rganlath3/PCB-Business-Card/Visual_Assetts/EnclosureUnpopulated.png

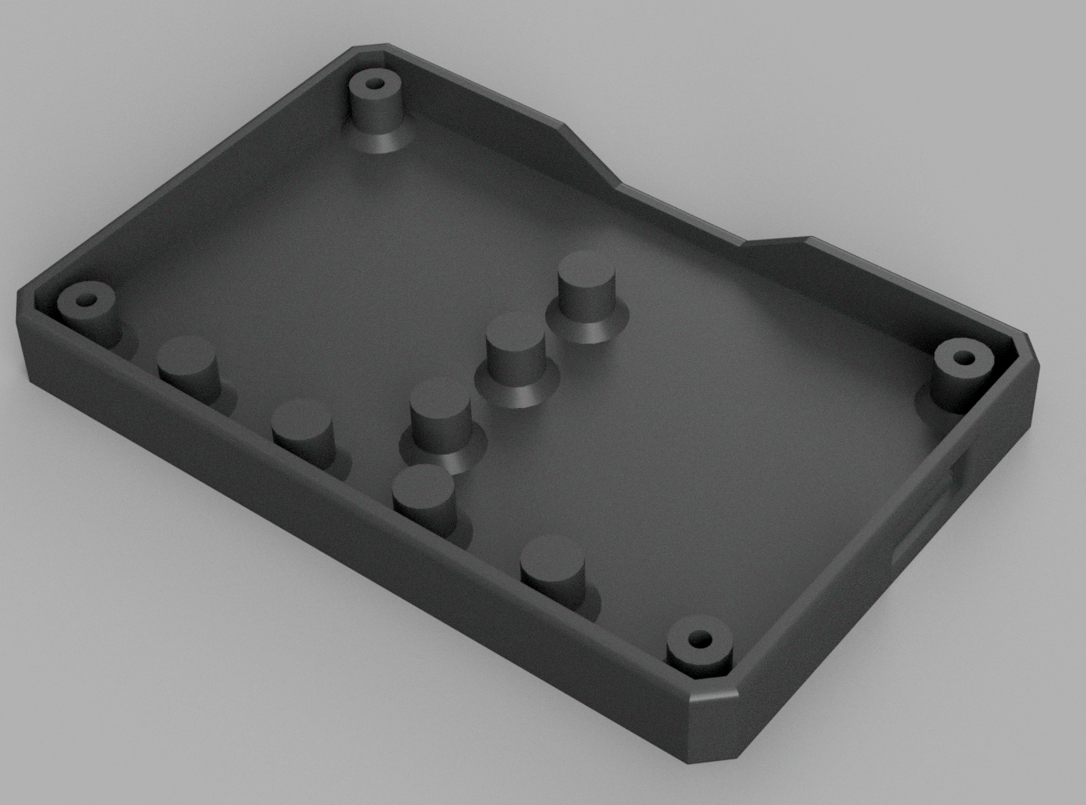
Visual_Assetts/EnclosureUnpopulated.png
