rganlath3/PCB-Business-Card/Visual_Assetts/MK1 Render Iso View 2.png

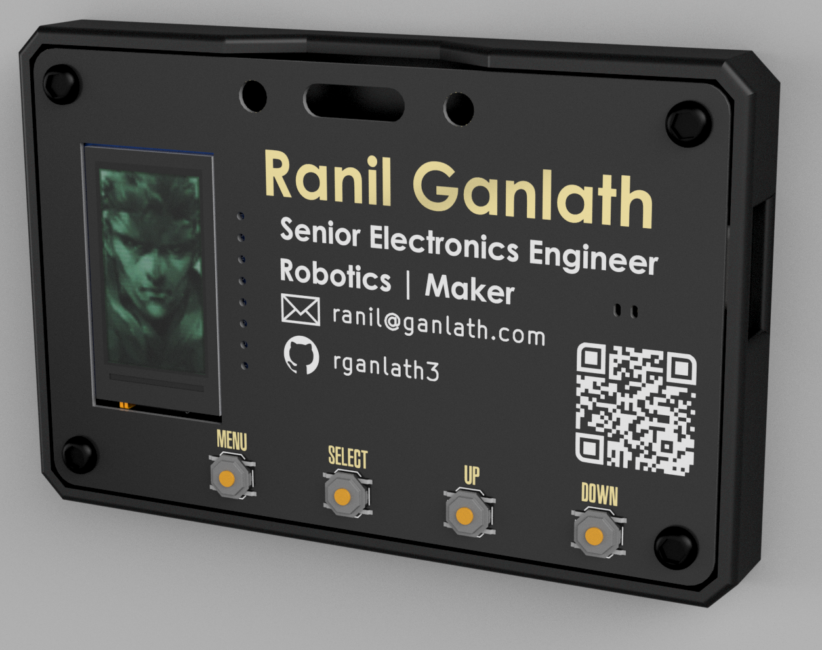
Visual_Assetts/MK1 Render Iso View 2.png
