rganlath3/PCB-Business-Card/MCU_Programming/ESP32-S3/3_Looping_Image_Display/OtaconB.h

// We need this header file to use FLASH as storage with PROGMEM directive:


const unsigned short  OB[] PROGMEM={
0x2c2a, 0x2c2a, 0x2c2a, 0x2c2a, 0x2c2a, 0x2c29, 0x2c29, 0x2c29, 0x2bc9, 0x2bc9, 0x2bc9, 0x23c8, 0x23c8, 0x1b47, 0x1b47, 0x1b47, 0x1b47, 0x1b47, 0x1b47, 0x2306, 0x2306, 0x2306, 0x1285, 0x1285, 0x1306, 0x1306, 0x1306, 0x1ac6, 0x1ac6, 0x1ac6, 0x0a04, 0x0a04, 0x12c5, 0x12c5, 0x12c5, 0x1ac6, 0x1ac6, 0x1ac6, 0x1306, 0x1306, 0x1ac6, 0x1ac6, 0x1ac6, 0x12c5, 0x12c5, 0x12c5, 0x1ac6, 0x1ac6, 0x1b47, 0x1b47, 0x1b47, 0x1b47, 0x1b47, 0x1b47, 0x2306, 0x2306, 0x2306, 0x1306, 0x1306, 0x2306, 0x2306, 0x2306, 0x1306, 0x1306, 0x1306, 0x1ac6, 0x1ac6, 0x12c5, 0x12c5, 0x12c5, 0x1244, 0x1244, 0x1244, 0x1a04, 0x1a04, 0x0a04, 0x0a04, 0x0a04, 0x1143, 0x1143, 0x1143, 0x0983, 0x0983, 0x0983, 0x0983, 0x0983, 0x0942, 0x0942, 0x0942, 0x0942, 0x0942, 0x0942, 0x0942, 0x0942, 0x0942, 0x0942, 0x0942, 0x0983, 0x0983, 0x0983, 0x0983, 0x0983, 0x0983, 0x0983, 0x0983, 0x11c4, 0x11c4, 0x11c4, 0x09c3, 0x09c3, 0x0983, 0x0983, 0x0983, 0x0983, 0x0983, 0x0983, 0x1a04, 0x1a04, 0x09c3, 0x09c3, 0x09c3, 0x0983, 0x0983, 0x0983, 0x0942, 0x0942, 0x0942, 0x0942, 0x0942, 0x0983, 0x0983, 0x0983, 0x2306, 0x2306, 0x2306, 0x12c5, 0x12c5, 0x1285, 0x1285, 0x1285, 
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
};
