rganlath3/PCB-Business-Card/MCU_Programming/ESP32-S3/3_Looping_Image_Display/OtaconS2.h

// We need this header file to use FLASH as storage with PROGMEM directive:


const unsigned short  O2[] PROGMEM={
0x23e8, 0x23e8, 0x1ba8, 0x1b87, 0x1b47, 0x1346, 0x1326, 0x1326, 0x1326, 0x1326, 0x1326, 0x1326, 0x1326, 0x1305, 0x12e5, 0x12e5, 0x12e5, 0x12e5, 0x12e5, 0x0ac4, 0x0aa4, 0x0aa4, 0x0aa4, 0x0ac4, 0x0ae5, 0x0b05, 0x0aa5, 0x0a65, 0x0a24, 0x0a04, 0x0223, 0x0243, 0x0a84, 0x0aa5, 0x0a85, 0x0a64, 0x0a23, 0x09e3, 0x0182, 0x0162, 0x0182, 0x01a2, 0x01a2, 0x01a2, 0x01a2, 0x01a2, 0x01a2, 0x01c2, 0x0a23, 0x0a64, 0x0a85, 0x0aa5, 0x0aa5, 0x0aa5, 0x0aa5, 0x0aa5, 0x0ac5, 0x0ae5, 0x0ae5, 0x0ac5, 0x0aa5, 0x0aa5, 0x0aa5, 0x0aa5, 0x0aa5, 0x0aa5, 0x0aa5, 0x0aa5, 0x0aa5, 0x0aa5, 0x0aa5, 0x0aa5, 0x0aa5, 0x0aa5, 0x0aa5, 0x0aa5, 0x0aa5, 0x0aa5, 0x0aa5, 0x0aa5, 0x0aa5, 0x0aa5, 0x0aa5, 0x0aa5, 0x0aa5, 0x0aa5, 0x0aa5, 0x0aa5, 0x0aa5, 0x0aa5, 0x0aa5, 0x0aa5, 0x0aa5, 0x0aa5, 0x0aa5, 0x0aa5, 0x0ac5, 0x12e5, 0x12e5, 0x1305, 0x12e5, 0x12e5, 0x12e5, 0x12e5, 0x1305, 0x1325, 0x1325, 0x1325, 0x1326, 0x1346, 0x1346, 0x1366, 0x1366, 0x1367, 0x1367, 0x1367, 0x1b67, 0x1b67, 0x1b67, 0x1b67, 0x1b87, 0x1b87, 0x1ba7, 0x1ba7, 0x1ba7, 0x1ba7, 0x1ba7, 0x1ba7, 0x1ba7, 0x1ba7, 0x1ba7, 0x1ba7, 0x1ba8, 0x1ba8, 0x1ba8, 0x1ba8, 0x1ba8, 0x1bc9, 0x23e9, 0x23e9, 
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
};
