rganlath3/PCB-Business-Card/MCU_Programming/ESP32-S3/3_Looping_Image_Display/OtaconS3.h

// We need this header file to use FLASH as storage with PROGMEM directive:


const unsigned short  O3[] PROGMEM={
0x12c6, 0x12c6, 0x12c6, 0x1b47, 0x1b47, 0x2388, 0x2388, 0x2388, 0x2388, 0x2388, 0x2388, 0x2388, 0x2388, 0x1b47, 0x1b47, 0x1b47, 0x1b47, 0x1b47, 0x1b47, 0x1b06, 0x1b06, 0x1b06, 0x1b07, 0x1b07, 0x1b06, 0x1b06, 0x1b06, 0x1b47, 0x1b47, 0x1b47, 0x1b47, 0x1b47, 0x0983, 0x0983, 0x0983, 0x0902, 0x0902, 0x0902, 0x09c3, 0x09c3, 0x09c3, 0x09c3, 0x09c3, 0x09c3, 0x09c3, 0x09c3, 0x1285, 0x1285, 0x12c6, 0x12c6, 0x12c6, 0x12c6, 0x12c6, 0x12c6, 0x12c6, 0x12c6, 0x12c6, 0x12c6, 0x12c6, 0x12c6, 0x12c6, 0x12c6, 0x12c6, 0x12c6, 0x12c6, 0x12c6, 0x12c6, 0x12c6, 0x12c6, 0x12c6, 0x12c6, 0x12c6, 0x12c6, 0x12c6, 0x12c6, 0x12c6, 0x12c6, 0x12c6, 0x12c6, 0x12c6, 0x12c6, 0x12c6, 0x12c6, 0x12c6, 0x12c6, 0x12c6, 0x12c6, 0x12c6, 0x12c6, 0x12c6, 0x12c6, 0x12c6, 0x12c6, 0x12c6, 0x12c6, 0x12c6, 0x12c6, 0x12c6, 0x12c6, 0x12c6, 0x12c6, 0x12c6, 0x1b47, 0x1b47, 0x1b47, 0x1b47, 0x1b47, 0x1b47, 0x1b87, 0x1b87, 0x1b87, 0x1b87, 0x1b87, 0x1b87, 0x1b87, 0x1b87, 0x2388, 0x2388, 0x23c8, 0x23c8, 0x23c8, 0x23c8, 0x23c8, 0x23c8, 0x23c9, 0x23c9, 0x23c9, 0x23c9, 0x23c9, 0x23c9, 0x23c9, 0x23c9, 0x23c9, 0x23c9, 0x23c9, 0x2bc9, 0x2bc9, 0x2c29, 0x2c29, 0x2c29, 
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
};
